erichexter/m2-airsoft-steel-core/cad/60_Print_Trigger.stp

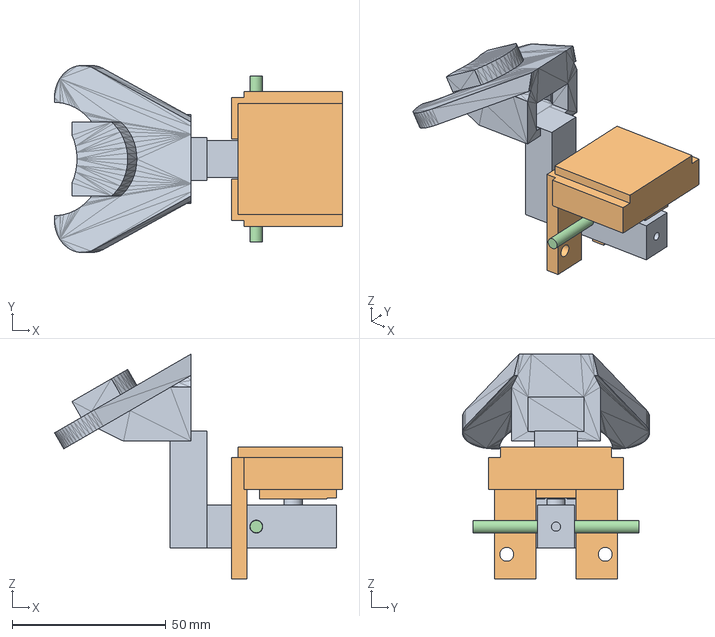
[picture p7: CAD file, 2026-09-14]
cad/60_Print_Trigger.stp
93.5 x 60.8 x 73.0 mm
