erichexter/m2-airsoft-steel-core/cad/30_Print_Barrel.stp

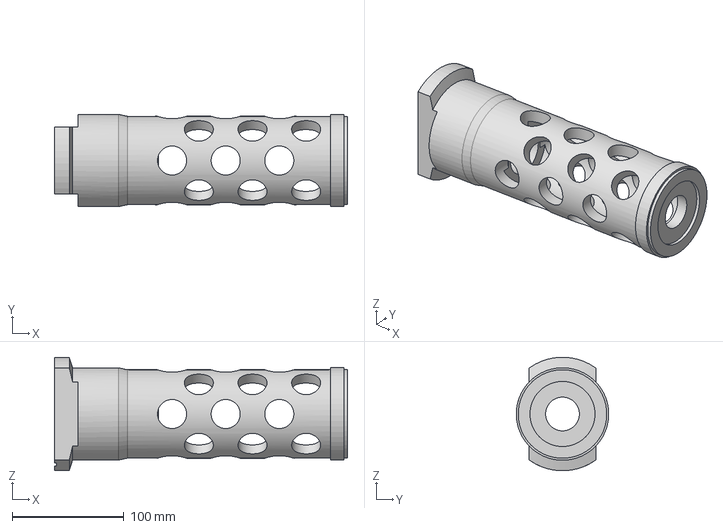
[picture p8: CAD file, 2026-09-14]
cad/30_Print_Barrel.stp
262.2 x 82.8 x 101.4 mm
