erichexter/m2-airsoft-steel-core/cad/11_Steel_Weldments.stp

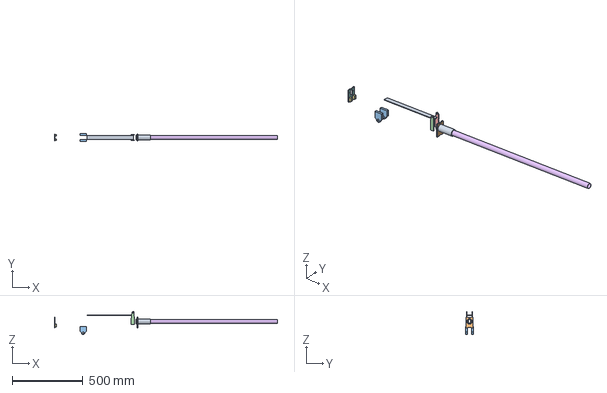
[picture p9: CAD file, 2026-09-14]
cad/11_Steel_Weldments.stp
1573.7 x 56.7 x 162.5 mm
