erichexter/m2-airsoft-steel-core/cad/M2_steel_core.stp

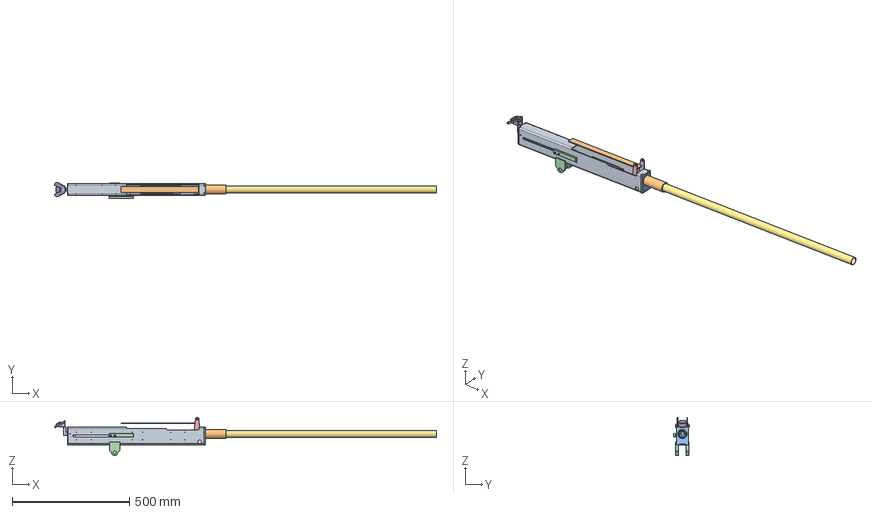
[picture p10: CAD file, 2026-09-12]
cad/M2_steel_core.stp
1628.0 x 68.4 x 162.5 mm
Core_Box_2x3_11ga
Steel_Weldments
Engine_Cradle
Charging_Handle
Trigger_Group
